MalphasWats/hawk/articles/screenshots/009-adding-power-symbols.png

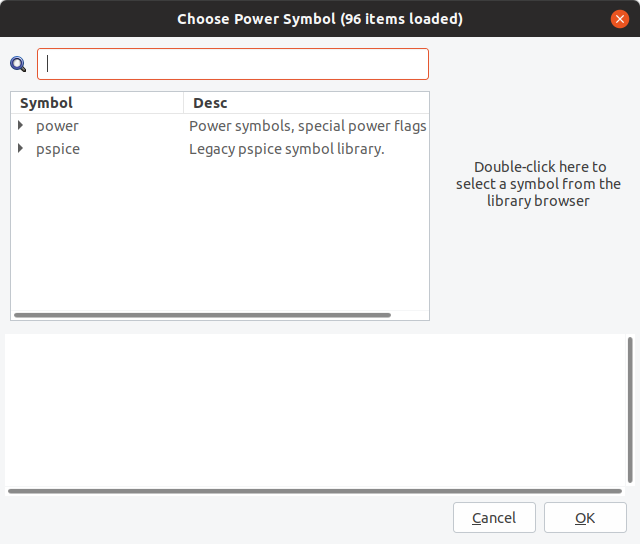
articles/screenshots/009-adding-power-symbols.png
