MalphasWats/hawk/oled/ASCII.h

#ifndef ASCII_H
#define ASCII_H

static const uint8_t ASCII[]  = {
    0x00, 0x00, 0x00, 0x00, 0x00, 0x00, 0x00, 0x00, // SPACE [ASCII - 32]
    // TODO: Define
    0x00, 0x00, 0x00, 0x00, 0x00, 0x00, 0x00, 0x00,  // !
	0x00, 0x00, 0x00, 0x00, 0x00, 0x00, 0x00, 0x00,  // "
	0x00, 0x00, 0x28, 0x7c, 0x28, 0x7c, 0x28, 0x00,  // #
	0x00, 0x00, 0x00, 0x00, 0x00, 0x00, 0x00, 0x00,  // $
	0x00, 0x00, 0x00, 0x00, 0x00, 0x00, 0x00, 0x00,  // %
	0x00, 0x00, 0x00, 0x00, 0x00, 0x00, 0x00, 0x00,  // &
	0x00, 0x00, 0x00, 0x00, 0x00, 0x00, 0x00, 0x00,  // '
	0x00, 0x00, 0x7e, 0x7e, 0xc3, 0xc3, 0x00, 0x00,  // (
	0x00, 0x00, 0xc3, 0xc3, 0x7e, 0x7e, 0x00, 0x00,  // )
	0x00, 0x00, 0x28, 0x10, 0x7c, 0x10, 0x28, 0x00,  // *
	0x00, 0x00, 0x00, 0x00, 0x00, 0x00, 0x00, 0x00,  // +
	0x00, 0x00, 0x00, 0x00, 0x00, 0x00, 0x00, 0x00,  // ,
	0x00, 0x00, 0x00, 0x00, 0x00, 0x00, 0x00, 0x00,  // -
	0x00, 0x00, 0x00, 0x00, 0x00, 0x00, 0x00, 0x00,  // .
	0x00, 0x00, 0x00, 0x00, 0x00, 0x00, 0x00, 0x00,  // /

	0x00, 0x7c, 0xfe, 0xb2, 0x9a, 0xfe, 0x7c, 0x00,  // 0  (16)
	0x00, 0x88, 0x8c, 0xfe, 0xfe, 0x80, 0x80, 0x00,  // 1
	0x00, 0xc4, 0xe6, 0xb2, 0x92, 0x9e, 0x8c, 0x00,  // 2
	0x00, 0x44, 0xc6, 0x92, 0x92, 0xfe, 0x6c, 0x00,  // 3
	0x00, 0x30, 0x38, 0x4c, 0xfe, 0xfe, 0x20, 0x00,  // 4
	0x00, 0x4e, 0xce, 0x8a, 0x8a, 0xfa, 0x72, 0x00,  // 5
	0x00, 0x78, 0xfc, 0x96, 0x92, 0xf2, 0x60, 0x00,  // 6
	0x00, 0x02, 0xe2, 0xf2, 0x1a, 0x0e, 0x06, 0x00,  // 7
	0x00, 0x6c, 0xfe, 0x92, 0x92, 0xfe, 0x6c, 0x00,  // 8
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
	0x00, 0x4e, 0xce, 0x8a, 0x8a, 0xfa, 0x72, 0x00,  // 5
	0x00, 0x78, 0xfc, 0x96, 0x92, 0xf2, 0x60, 0x00,  // 6
	0x00, 0x02, 0xe2, 0xf2, 0x1a, 0x0e, 0x06, 0x00,  // 7
	0x00, 0x6c, 0xfe, 0x92, 0x92, 0xfe, 0x6c, 0x00,  // 8
	0x00, 0x0c, 0x9e, 0x92, 0xd2, 0x7e, 0x3c, 0x00,  // 9
};

#endif
